warmhammer/eurobot_23/catkin_ws/src/dolly_navigation/maps/blue_map.png

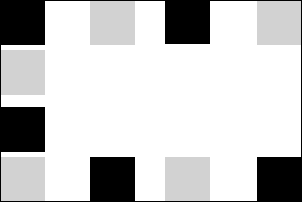
catkin_ws/src/dolly_navigation/maps/blue_map.png
