warmhammer/eurobot_23/stm32_ws/Eurobot2023/Drivers/VL53L0X_API/platform/src/vl53l0x_platform.c

/*******************************************************************************
Copyright � 2015, STMicroelectronics International N.V.
All rights reserved.

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
THIS SOFTWARE IS PROVIDED BY THE COPYRIGHT HOLDERS AND CONTRIBUTORS "AS IS" AND
ANY EXPRESS OR IMPLIED WARRANTIES, INCLUDING, BUT NOT LIMITED TO, THE IMPLIED
WARRANTIES OF MERCHANTABILITY, FITNESS FOR A PARTICULAR PURPOSE, AND
NON-INFRINGEMENT OF INTELLECTUAL PROPERTY RIGHTS ARE DISCLAIMED.
IN NO EVENT SHALL STMICROELECTRONICS INTERNATIONAL N.V. BE LIABLE FOR ANY
DIRECT, INDIRECT, INCIDENTAL, SPECIAL, EXEMPLARY, OR CONSEQUENTIAL DAMAGES
(INCLUDING, BUT NOT LIMITED TO, PROCUREMENT OF SUBSTITUTE GOODS OR SERVICES;
LOSS OF USE, DATA, OR PROFITS; OR BUSINESS INTERRUPTION) HOWEVER CAUSED AND
ON ANY THEORY OF LIABILITY, WHETHER IN CONTRACT, STRICT LIABILITY, OR TORT
(INCLUDING NEGLIGENCE OR OTHERWISE) ARISING IN ANY WAY OUT OF THE USE OF THIS
SOFTWARE, EVEN IF ADVISED OF THE POSSIBILITY OF SUCH DAMAGE.
********************************************************************************/

/**
 * @file VL53L0X_i2c.c
 *
 * Copyright (C) 2014 ST MicroElectronics
 *
 * provide variable word size byte/Word/dword VL6180x register access via i2c
 *
 */
#include "vl53l0x_platform.h"
#include "vl53l0x_i2c_platform.h"
#include "vl53l0x_api.h"

#include <string.h>

#define LOG_FUNCTION_START(fmt, ... )           _LOG_FUNCTION_START(TRACE_MODULE_PLATFORM, fmt, ##__VA_ARGS__)
#define LOG_FUNCTION_END(status, ... )          _LOG_FUNCTION_END(TRACE_MODULE_PLATFORM, status, ##__VA_ARGS__)
#define LOG_FUNCTION_END_FMT(status, fmt, ... ) _LOG_FUNCTION_END_FMT(TRACE_MODULE_PLATFORM, status, fmt, ##__VA_ARGS__)

/**
 * @def I2C_BUFFER_CONFIG
 *
 * @brief Configure Device register I2C access
 *
 * @li 0 : one GLOBAL buffer \n
 *   Use one global buffer of MAX_I2C_XFER_SIZE byte in data space \n
 *   This solution is not multi-Device compliant nor multi-thread cpu safe \n
 *   It can be the best option for small 8/16 bit MCU without stack and limited ram  (STM8s, 80C51 ...)
 *
 * @li 1 : ON_STACK/local \n
 *   Use local variable (on stack) buffer \n
 *   This solution is multi-thread with use of i2c resource lock or mutex see VL6180x_GetI2CAccess() \n
 *
 * @li 2 : User defined \n
 *    Per Device potentially dynamic allocated. Requires VL6180x_GetI2cBuffer() to be implemented.
 * @ingroup Configuration
 */
#define I2C_BUFFER_CONFIG 1
/** Maximum buffer size to be used in i2c */
#define VL53L0X_MAX_I2C_XFER_SIZE   64 /* Maximum buffer size to be used in i2c */

#if I2C_BUFFER_CONFIG == 0
    /* GLOBAL config buffer */
    uint8_t i2c_global_buffer[VL53L0X_MAX_I2C_XFER_SIZE];

    #define DECL_I2C_BUFFER
    #define VL53L0X_GetLocalBuffer(Dev, n_byte)  i2c_global_buffer

#elif I2C_BUFFER_CONFIG == 1
    /* ON STACK */
    #define DECL_I2C_BUFFER  uint8_t LocBuffer[VL53L0X_MAX_I2C_XFER_SIZE];
    #define VL53L0X_GetLocalBuffer(Dev, n_byte)  LocBuffer
#elif I2C_BUFFER_CONFIG == 2
    /* user define buffer type declare DECL_I2C_BUFFER  as access  via VL53L0X_GetLocalBuffer */
    #define DECL_I2C_BUFFER
#else
#error "invalid I2C_BUFFER_CONFIG "
#endif


#define VL53L0X_I2C_USER_VAR         /* none but could be for a flag var to get/pass to mutex interruptible  return flags and try again */
#define VL53L0X_GetI2CAccess(Dev)    /* todo mutex acquire */
#define VL53L0X_DoneI2CAcces(Dev)    /* todo mutex release */

#define I2C_TIME_OUT_BASE   10
#define I2C_TIME_OUT_BYTE   1

#define VL53L0X_OsDelay(...) HAL_Delay(2)

uint8_t _I2CBuffer[VL53L0X_MAX_I2C_XFER_SIZE];                  //MAX size of I2C Buffer

int _I2CWrite(VL53L0X_DEV Dev, uint8_t *pdata, uint32_t count) {
    int status;
    int i2c_time_out = I2C_TIME_OUT_BASE+ count* I2C_TIME_OUT_BYTE;

    status = HAL_I2C_Master_Transmit(Dev->I2cHandle, Dev->I2cDevAddr, pdata, count, i2c_time_out);
    if (status) {
        //error
    }
    return status;
}

int _I2CRead(VL53L0X_DEV Dev, uint8_t *pdata, uint32_t count) {
    int status;
    int i2c_time_out = I2C_TIME_OUT_BASE+ count* I2C_TIME_OUT_BYTE;

    status = HAL_I2C_Master_Receive(Dev->I2cHandle, Dev->I2cDevAddr|1, pdata, count, i2c_time_out);
    if (status) {
        //error
    }
    return status;
}


VL53L0X_Error VL53L0X_LockSequenceAccess(VL53L0X_DEV Dev){
    VL53L0X_Error Status = VL53L0X_ERROR_NONE;

    return Status;
}

VL53L0X_Error VL53L0X_UnlockSequenceAccess(VL53L0X_DEV Dev){
    VL53L0X_Error Status = VL53L0X_ERROR_NONE;

    return Status;
}

// the ranging_sensor_comms.dll will take care of the page selection
VL53L0X_Error VL53L0X_WriteMulti(VL53L0X_DEV Dev, uint8_t index, uint8_t *pdata, uint32_t count){
    int status_int;
    VL53L0X_Error Status = VL53L0X_ERROR_NONE;
    if (count > sizeof(_I2CBuffer) - 1) {
            return VL53L0X_ERROR_INVALID_PARAMS;
        }
    _I2CBuffer[0] = index;
    memcpy(&_I2CBuffer[1], pdata, count);

    status_int = _I2CWrite(Dev, _I2CBuffer, count + 1);
    if (status_int != 0) {
            Status = VL53L0X_ERROR_CONTROL_INTERFACE;
        }
    return Status;
}

// the ranging_sensor_comms.dll will take care of the page selection
VL53L0X_Error VL53L0X_ReadMulti(VL53L0X_DEV Dev, uint8_t index, uint8_t *pdata, uint32_t count){
    VL53L0X_Error Status = VL53L0X_ERROR_NONE;
    int32_t status_int;

    status_int = _I2CWrite(Dev, &index, 1);
    if (status_int != 0) {
            Status = VL53L0X_ERROR_CONTROL_INTERFACE;
            return Status;
        }
    status_int = _I2CRead(Dev, pdata, count);
    if (status_int != 0) {
            Status = VL53L0X_ERROR_CONTROL_INTERFACE;
        }
    return Status;
}

VL53L0X_Error VL53L0X_WrByte(VL53L0X_DEV Dev, uint8_t index, uint8_t data){
    VL53L0X_Error Status = VL53L0X_ERROR_NONE;
    int32_t status_int;

    _I2CBuffer[0] = index;
    _I2CBuffer[1] = data;

    status_int = _I2CWrite(Dev, _I2CBuffer, 2);
    if (status_int != 0) {
        Status = VL53L0X_ERROR_CONTROL_INTERFACE;
    }

    return Status;
}

VL53L0X_Error VL53L0X_WrWord(VL53L0X_DEV Dev, uint8_t index, uint16_t data){
    VL53L0X_Error Status = VL53L0X_ERROR_NONE;
    int32_t status_int;

    _I2CBuffer[0] = index;
    _I2CBuffer[1] = data >> 8;
    _I2CBuffer[2] = data & 0x00FF;

    status_int = _I2CWrite(Dev, _I2CBuffer, 3);
    if (status_int != 0) {
        Status = VL53L0X_ERROR_CONTROL_INTERFACE;
    }
    return Status;
}

VL53L0X_Error VL53L0X_WrDWord(VL53L0X_DEV Dev, uint8_t index, uint32_t data){
    VL53L0X_Error Status = VL53L0X_ERROR_NONE;
    int32_t status_int;
    _I2CBuffer[0] = index;
    _I2CBuffer[1] = (data >> 24) & 0xFF;
    _I2CBuffer[2] = (data >> 16) & 0xFF;
    _I2CBuffer[3] = (data >> 8)  & 0xFF;
    _I2CBuffer[4] = (data >> 0 ) & 0xFF;
    status_int = _I2CWrite(Dev, _I2CBuffer, 5);
    if (status_int != 0) {
        Status = VL53L0X_ERROR_CONTROL_INTERFACE;
    }
    return Status;
}

VL53L0X_Error VL53L0X_UpdateByte(VL53L0X_DEV Dev, uint8_t index, uint8_t AndData, uint8_t OrData){
    VL53L0X_Error Status = VL53L0X_ERROR_NONE;
    uint8_t data;

    Status = VL53L0X_RdByte(Dev, index, &data);
    if (Status) {
        return Status;
    }
    data = (data & AndData) | OrData;
    Status = VL53L0X_WrByte(Dev, index, data);
    return Status;
}

VL53L0X_Error VL53L0X_RdByte(VL53L0X_DEV Dev, uint8_t index, uint8_t *data){
    VL53L0X_Error Status = VL53L0X_ERROR_NONE;
    int32_t status_int;

    status_int = _I2CWrite(Dev, &index, 1);
    if( status_int ){
        Status = VL53L0X_ERROR_CONTROL_INTERFACE;
        return Status;
    }
    status_int = _I2CRead(Dev, data, 1);
    if (status_int != 0) {
        Status = VL53L0X_ERROR_CONTROL_INTERFACE;
    }

    return Status;
}

VL53L0X_Error VL53L0X_RdWord(VL53L0X_DEV Dev, uint8_t index, uint16_t *data){
    VL53L0X_Error Status = VL53L0X_ERROR_NONE;
    int32_t status_int;

    status_int = _I2CWrite(Dev, &index, 1);

    if( status_int ){
        Status = VL53L0X_ERROR_CONTROL_INTERFACE;
        return Status;
    }
    status_int = _I2CRead(Dev, _I2CBuffer, 2);
    if (status_int != 0) {
        Status = VL53L0X_ERROR_CONTROL_INTERFACE;
        return Status;
    }

    *data = ((uint16_t)_I2CBuffer[0]<<8) + (uint16_t)_I2CBuffer[1];
    return Status;
}

VL53L0X_Error  VL53L0X_RdDWord(VL53L0X_DEV Dev, uint8_t index, uint32_t *data){
    VL53L0X_Error Status = VL53L0X_ERROR_NONE;
    int32_t status_int;

    status_int = _I2CWrite(Dev, &index, 1);
    if (status_int != 0) {
        Status = VL53L0X_ERROR_CONTROL_INTERFACE;
        return Status;
    }
    status_int = _I2CRead(Dev, _I2CBuffer, 4);
    if (status_int != 0) {
        Status = VL53L0X_ERROR_CONTROL_INTERFACE;
        return Status;
    }

    *data = ((uint32_t)_I2CBuffer[0]<<24) + ((uint32_t)_I2CBuffer[1]<<16) + ((uint32_t)_I2CBuffer[2]<<8) + (uint32_t)_I2CBuffer[3];
    return Status;
}

#define VL53L0X_POLLINGDELAY_LOOPNB  250
VL53L0X_Error VL53L0X_PollingDelay(VL53L0X_DEV Dev){
    VL53L0X_Error status = VL53L0X_ERROR_NONE;

    // do nothing
    VL53L0X_OsDelay();
    return status;
}
