warmhammer/eurobot_23/catkin_ws/src/dolly_base/src/stm_topic_converter.cpp

#include <ros/ros.h>
#include <std_msgs/Float64.h>
#include <std_msgs/Float32.h>

void leftWheelCallback(const std_msgs::Float64& cmd_vel);
void rightWheelCallback(const std_msgs::Float64& cmd_vel);
void left_Wheel_Cur_Vel_Callback(const std_msgs::Float32& cur_vel);
void right_Wheel_Cur_Vel_Callback(const std_msgs::Float32& cur_vel);

ros::Publisher left_wheel_pub;
ros::Publisher right_wheel_pub; //CMD Pub

ros::Publisher left_wheel_cur_vel_pub;
ros::Publisher right_wheel_cur_vel_pub;

ros::Subscriber left_wheel_sub;
ros::Subscriber right_wheel_sub; //CMD Sub

ros::Subscriber left_wheel_cur_vel_sub;
ros::Subscriber right_wheel_cur_vel_sub;

int main(int argc, char* argv[]) {
    ros::init(argc, argv, "stm_topic_converter");
	ros::NodeHandle node;

    left_wheel_sub = node.subscribe("/dolly/left_wheel/pwd64", 1, leftWheelCallback);
    right_wheel_sub = node.subscribe("/dolly/right_wheel/pwd64", 1, rightWheelCallback);

    left_wheel_cur_vel_sub = node.subscribe("/dolly/left_wheel/cur_vel32",1,left_Wheel_Cur_Vel_Callback);
    right_wheel_cur_vel_sub = node.subscribe("/dolly/right_wheel/cur_vel32",1,right_Wheel_Cur_Vel_Callback);

    left_wheel_pub = node.advertise<std_msgs::Float32>("/dolly/left_wheel/pwd32", 1);
    right_wheel_pub = node.advertise<std_msgs::Float32>("/dolly/right_wheel/pwd32", 1);

    left_wheel_cur_vel_pub = node.advertise<std_msgs::Float64>("dolly/left_wheel/cur_vel64",1);
    right_wheel_cur_vel_pub = node.advertise<std_msgs::Float64>("dolly/right_wheel/cur_vel64",1);


    ros::spin();

	return 0;
}

void leftWheelCallback(const std_msgs::Float64& cmd_vel) {
    std_msgs::Float32 converted;
    converted.data = cmd_vel.data;

    left_wheel_pub.publish(converted);
}

void rightWheelCallback(const std_msgs::Float64& cmd_vel) {
    std_msgs::Float32 converted;
    converted.data = cmd_vel.data;

    right_wheel_pub.publish(converted);
}

void left_Wheel_Cur_Vel_Callback(const std_msgs::Float32& cur_vel){
    std_msgs::Float64 converted;
    converted.data = cur_vel.data;

    left_wheel_cur_vel_pub.publish(converted);
}

void right_Wheel_Cur_Vel_Callback(const std_msgs::Float32& cur_vel){
    std_msgs::Float64 converted;
    converted.data = cur_vel.data;

    right_wheel_cur_vel_pub.publish(converted);
}
